EsTaNG9/freertos-ecu/pics/avanço.png

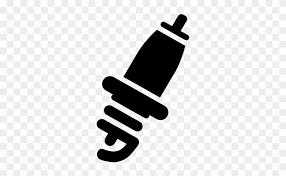
pics/avanço.png
