EsTaNG9/freertos-ecu/pics/engine_temp.png

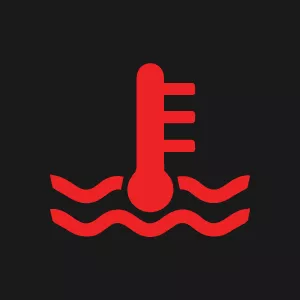
pics/engine_temp.png
