EsTaNG9/freertos-ecu/pics/images.jpg

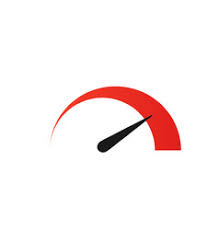
pics/images.jpg
