EsTaNG9/freertos-ecu/pics/istockphoto-1371014378-612x612.jpg

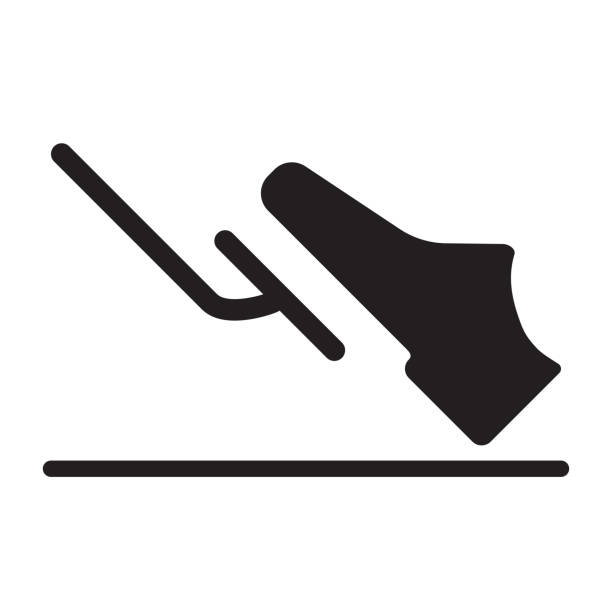
pics/istockphoto-1371014378-612x612.jpg
