EsTaNG9/freertos-ecu/logo_rpm.h

#ifndef LOGO_RPM_H
#define LOGO_RPM_H

// logo temp_motor em bitmap
const uint16_t logo_rpm[] PROGMEM ={
		 0x0000, 0x0000, 0x0000, 0x0000, 0x0000, 0x0000, 0x0000, 0x0000, 0x0000, 0x0000, 0x0000, 0x0000, 0x0000, 0x0000, 0x0000, 0x0000, 0x0000, 0x0000, 0x0000, 0x0000, 0x0000, 0x0000, 0x0000, 0x0000, 0x0000, 0x0000, 0x0800, 0x1820, 0x3841, 0x4861, 0x6082, 0x78c3, 0x80a3, 0x8082, 0x8082, 0x88e3, 0x9986, 0xb186, 0xb186, 0x9986, 0x9986, 0x88e3, 0x80c3, 0x80c3, 0x68c3, 0x50a2, 0x4041, 0x2841, 0x1020, 0x0000, 0x0000, 0x0000, 0x0000, 0x0000, 0x0000, 0x0000, 0x0000, 0x0000, 0x0000, 0x0000, 0x0000, 0x0000, 0x0000, 0x0000, 0x0000, 0x0000, 0x0000, 0x0000, 0x0000, 0x0000, 0x0000, 0x0000, 0x0000, 0x0000, 0x0000, 0x0000, 0x0000, 0x0000,
		  0x0000, 0x0000, 0x0000, 0x0000, 0x0000, 0x0000, 0x0000, 0x0000, 0x0000, 0x0000, 0x0000, 0x0000, 0x0000, 0x0000, 0x0000, 0x0000, 0x0000, 0x0000, 0x0000, 0x0000, 0x0000, 0x0000, 0x1000, 0x1820, 0x2020, 0x2841, 0x4041, 0x5061, 0x6082, 0x7882, 0x88c3, 0x98c3, 0xa0a3, 0xa0a3, 0xa0c3, 0xa0e3, 0xb104, 0xb186, 0xb186, 0xb186, 0xb104, 0xa0e3, 0xa0c3, 0x98c3, 0x88c3, 0x78c3, 0x6882, 0x5882, 0x4861, 0x3841, 0x2841, 0x2020, 0x1820, 0x0800, 0x0000, 0x0000, 0x0000, 0x0000, 0x0000, 0x0000, 0x0000, 0x0000, 0x0000, 0x0000, 0x0000, 0x0000, 0x0000, 0x0000, 0x0000, 0x0000, 0x0000, 0x0000, 0x0000, 0x0000, 0x0000, 0x0000, 0x0000, 0x0000,
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
		};
#endif
